comcat/iDuoDuo/firmware/power_avr.cpp

/* trackuino copyright (C) 2010  EA5HAV Javi
 *
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
 * You should have received a copy of the GNU General Public License
 * along with this program; if not, write to the Free Software
 * Foundation, Inc., 51 Franklin Street, Fifth Floor, Boston, MA  02110-1301, USA.
 */
#ifdef AVR

#include <avr/power.h>
#include <avr/signal.h>
#include <avr/sleep.h>
#include <WProgram.h>
#include "config.h"
#include "pin.h"
#include "power.h"

void disable_bod_and_sleep()
{
  /* This will turn off brown-out detection while
   * sleeping. Unfortunately this won't work in IDLE mode.
   * Relevant info about BOD disabling: datasheet p.44
   *
   * Procedure to disable the BOD:
   *
   * 1. BODSE and BODS must be set to 1
   * 2. Turn BODSE to 0
   * 3. BODS will automatically turn 0 after 4 cycles
   *
   * The catch is that we *must* go to sleep between 2
   * and 3, ie. just before BODS turns 0.
   */
  unsigned char mcucr;

  cli();
  mcucr = MCUCR | (_BV(BODS) | _BV(BODSE));
  MCUCR = mcucr;
  MCUCR = mcucr & (~_BV(BODSE));
  sei();
  sleep_mode();    // Go to sleep
}

void power_save()
{
  /* Enter power saving mode. SLEEP_MODE_IDLE is the least saving
   * mode, but it's the only one that will keep the UART running.
   * In addition, we need timer0 to keep track of time, timer 1
   * to drive the buzzer and timer2 to keep pwm output at its rest
   * voltage.
   */

  set_sleep_mode(SLEEP_MODE_IDLE);
  sleep_enable();
  power_adc_disable();
  power_spi_disable();
  power_twi_disable();

  //pin_write(LED_PIN, LOW);
  sleep_mode();    // Go to sleep
  //pin_write(LED_PIN, HIGH);
  
  sleep_disable();  // Resume after wake up
  power_all_enable();
}


#endif // #ifdef AVR
